OklahomaOpenSourceHardware/Oklahoma-Open-Hardware-Mechanical-Keyboard/Mechanical/1d330ba3ae6bdd7f7d86c17163a86d3b664da0f7_bottom.dxf

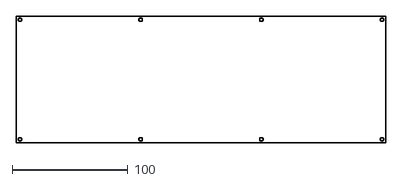
[picture p15: CAD file, 2022-06-14]
Mechanical/1d330ba3ae6bdd7f7d86c17163a86d3b664da0f7_bottom.dxf
318.8 x 109.2
