OklahomaOpenSourceHardware/Oklahoma-Open-Hardware-Mechanical-Keyboard/keyswitch-kicad-library-main/source_3d/Mounting_Keyboard_Stabilizer/Stabilizer_Cherry_MX_2u.FCStd

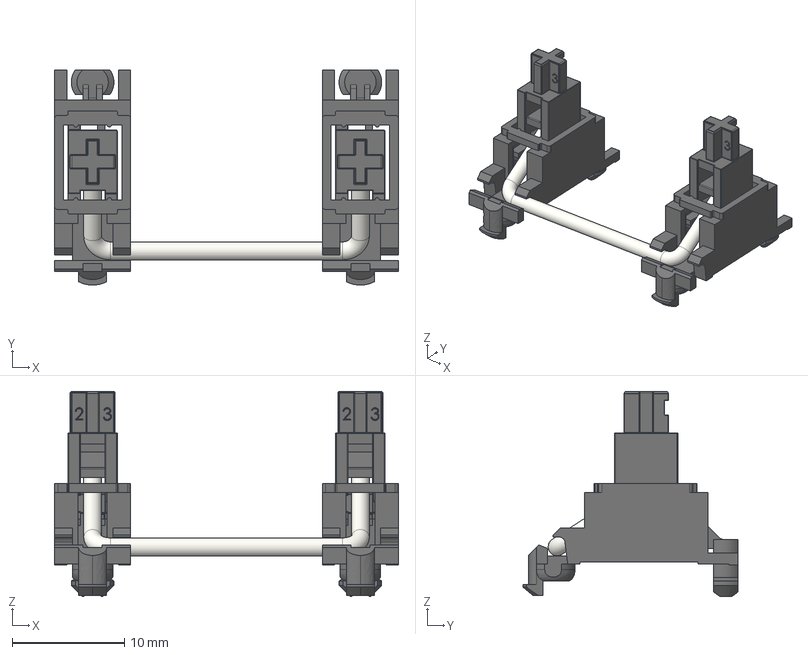
[picture p16: CAD file, 2022-06-28]
keyswitch-kicad-library-main/source_3d/Mounting_Keyboard_Stabilizer/Stabilizer_Cherry_MX_2u.FCStd
30.7 x 19.2 x 18.3 mm
Bar
Stabilizer_Key_
Stabilizer_Base_
Stabilizer_Key
Stabilizer_Base
